mars3142/warnemuende-lighthouses/firmware/components/remote_control/include/led_service.h

#pragma once

#include "host/ble_hs.h"
#include <stdio.h>

/// LED Service Characteristic Callbacks
int led_write(uint16_t conn_handle, uint16_t attr_handle, struct ble_gatt_access_ctxt *ctxt, void *arg);
int led_capabilities_read(uint16_t conn_handle, uint16_t attr_handle, struct ble_gatt_access_ctxt *ctxt, void *arg);

/// LED Service Characteristic User Description
int led_char_a000_user_desc(uint16_t con_handle, uint16_t attr_handle, struct ble_gatt_access_ctxt *ctxt, void *arg);
int led_char_dead_user_desc(uint16_t con_handle, uint16_t attr_handle, struct ble_gatt_access_ctxt *ctxt, void *arg);
